normanzb/g310gs/release/22_04_25/mudguard alt right.stl

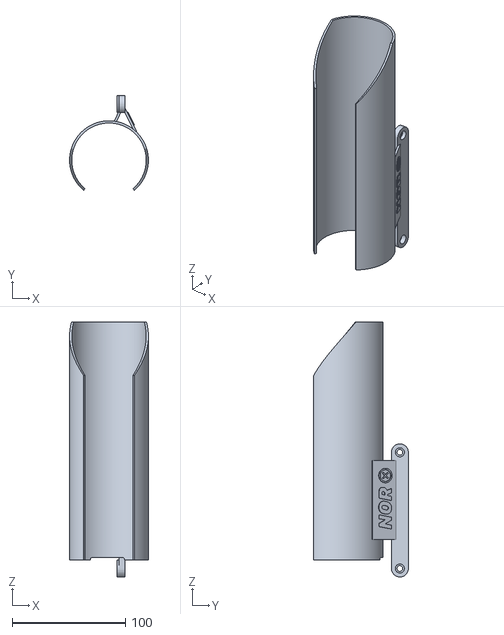
[picture p28: CAD file, 2022-04-25]
release/22_04_25/mudguard alt right.stl
69.6 x 83.6 x 225.0
