normanzb/g310gs/release/23_03_24/radiator guard.stl

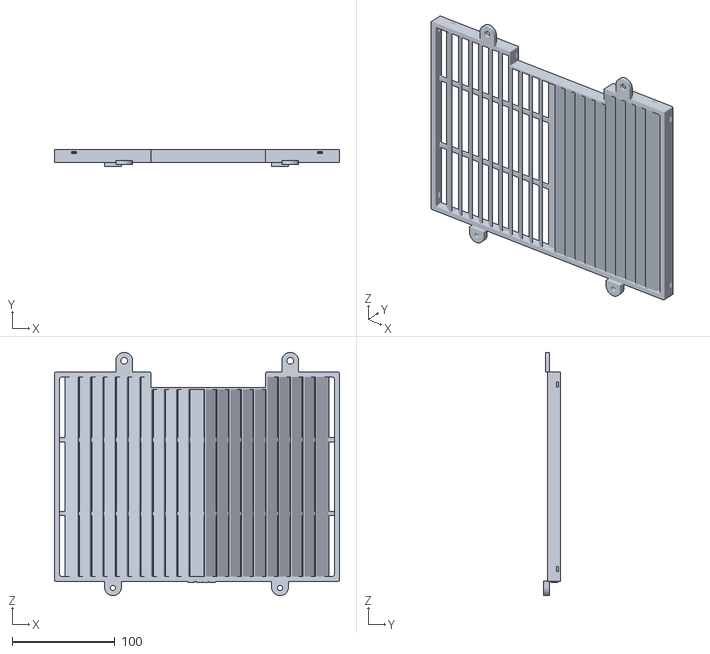
[picture p29: CAD file, 2023-03-10]
release/23_03_24/radiator guard.stl
278.0 x 17.0 x 237.2
