normanzb/g310gs/release/23_06_17/mudguard alt right.stl

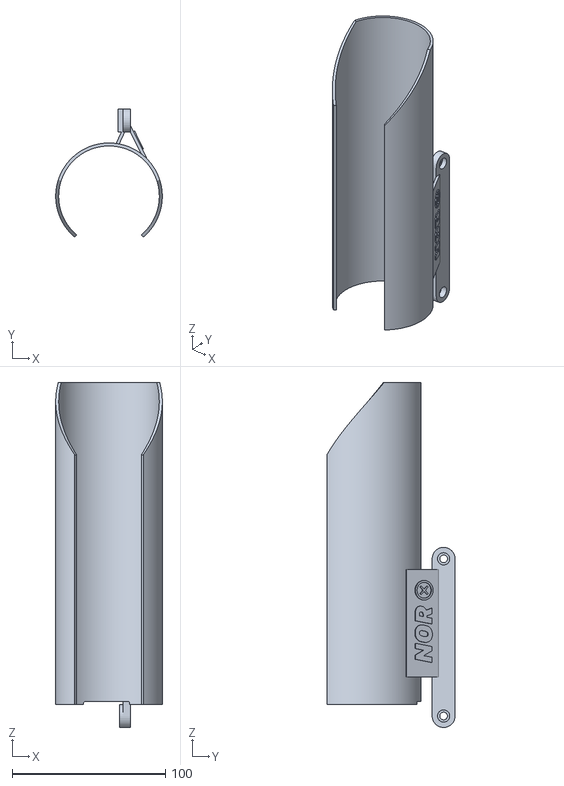
[picture p30: CAD file, 2022-11-01]
release/23_06_17/mudguard alt right.stl
69.6 x 83.6 x 225.0
