normanzb/g310gs/release/22_04_25/brake riser.stl

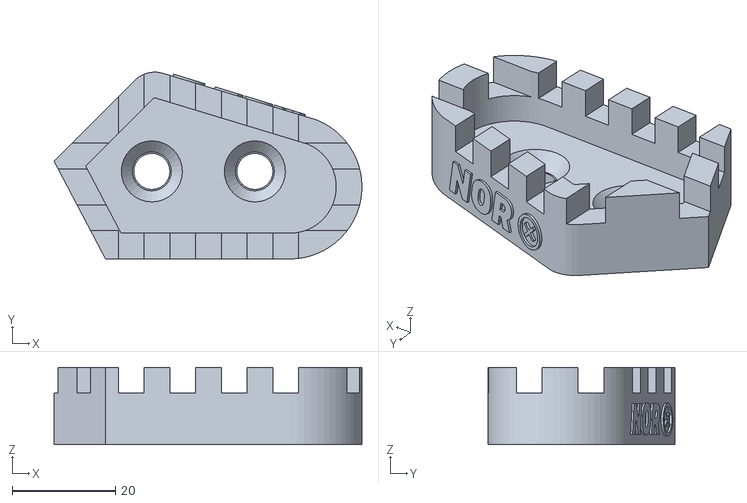
[picture p31: CAD file, 2022-04-25]
release/22_04_25/brake riser.stl
59.8 x 36.3 x 15.0
