normanzb/g310gs/release/23_03_24/mudguard_alt_left_rally_raid_lvl2.stl

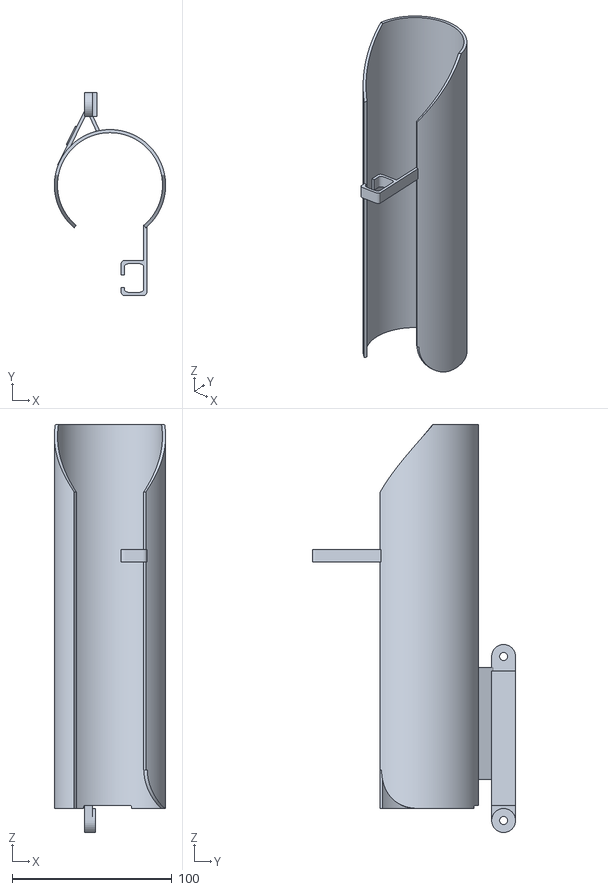
[picture p32: CAD file, 2023-01-09]
release/23_03_24/mudguard_alt_left_rally_raid_lvl2.stl
69.6 x 127.0 x 255.0
