normanzb/g310gs/release/23_03_24/mudguard_alt_right_rally_raid_lvl2.stl

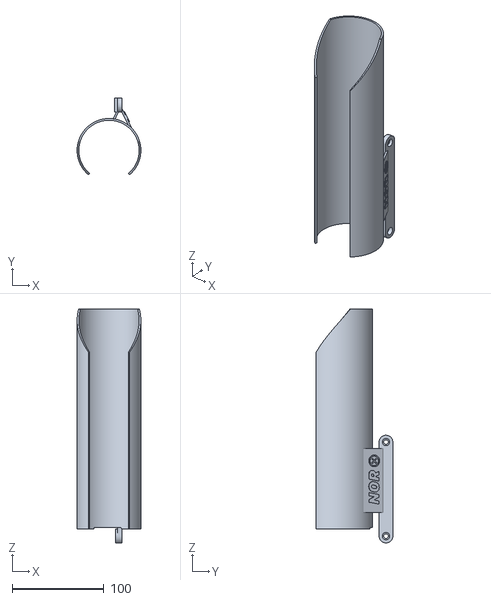
[picture p33: CAD file, 2023-01-09]
release/23_03_24/mudguard_alt_right_rally_raid_lvl2.stl
69.6 x 83.6 x 255.0
